jomendietad/access-control-stm32-esp32/esp32-s3-control-access-final/main/bsp/bsp_web.h

#ifndef BSP_WEB_H
#define BSP_WEB_H

#include <stdbool.h>

void BSP_Web_StartServer(void);
void BSP_Web_StopServer(void);
bool BSP_Web_IsResetRequested(void);
void BSP_Web_ClearResetRequest(void);

#endif /* BSP_WEB_H */
