jomendietad/access-control-stm32-esp32/esp32-s3-control-access-final/main/bsp/bsp_wifi.c

#include "bsp/bsp_wifi.h"
#include "esp_wifi.h"
#include "nvs_flash.h"
#include "esp_event.h"
#include "secrets/secrets.h"

static bool wifi_connected = false;

static void wifi_event_handler(void* arg, esp_event_base_t event_base, int32_t event_id, void* event_data) 
{
    if (event_base == WIFI_EVENT && event_id == WIFI_EVENT_STA_START) 
    {
        esp_wifi_connect();
    } 
    else if (event_base == WIFI_EVENT && event_id == WIFI_EVENT_STA_DISCONNECTED) 
    {
        wifi_connected = false;
        esp_wifi_connect();
    } 
    else if (event_base == IP_EVENT && event_id == IP_EVENT_STA_GOT_IP) 
    {
        wifi_connected = true;
    }
}

void BSP_WiFi_Init(void) 
{
    esp_netif_init();
    esp_event_loop_create_default();
    esp_netif_create_default_wifi_sta();
    
    wifi_init_config_t cfg = WIFI_INIT_CONFIG_DEFAULT();
    esp_wifi_init(&cfg);
    
    esp_event_handler_instance_register(WIFI_EVENT, ESP_EVENT_ANY_ID, &wifi_event_handler, NULL, NULL);
    esp_event_handler_instance_register(IP_EVENT, IP_EVENT_STA_GOT_IP, &wifi_event_handler, NULL, NULL);
    
    wifi_config_t wifi_config = {
        .sta = {
            .ssid = WIFI_SSID,
            .password = WIFI_PASS
        }
    };
    
    esp_wifi_set_mode(WIFI_MODE_STA);
    esp_wifi_set_config(WIFI_IF_STA, &wifi_config);
    esp_wifi_start();
}

bool BSP_WiFi_IsConnected(void) 
{
    return wifi_connected;
}
