jomendietad/access-control-stm32-esp32/stm32-nucleo-l476rg-control-access/src/bsp/bsp_placa.c

#include "bsp/bsp_placa.h"
#include "stm32l4xx_hal.h"
#include "bsp/bsp_uart.h"
#include "bsp/bsp_gpio.h"
#include "bsp/bsp_rfid.h"
#include "bsp/bsp_display.h"

static void SystemClock_Config(void);

void BSP_Init(void) {
    HAL_Init();
    SystemClock_Config();
    BSP_GPIO_Init();
    BSP_UART_Init();
    BSP_RFID_Init();
    BSP_Display_Init();
}

uint32_t BSP_GetTicks(void) {
    return HAL_GetTick();
}

static void SystemClock_Config(void) {
    RCC_OscInitTypeDef RCC_OscInitStruct = {0};
    RCC_ClkInitTypeDef RCC_ClkInitStruct = {0};

    RCC_OscInitStruct.OscillatorType = RCC_OSCILLATORTYPE_MSI;
    RCC_OscInitStruct.MSIState = RCC_MSI_ON;
    RCC_OscInitStruct.MSICalibrationValue = 0;
    RCC_OscInitStruct.MSIClockRange = RCC_MSIRANGE_6; // 4 MHz
    RCC_OscInitStruct.PLL.PLLState = RCC_PLL_ON;
    RCC_OscInitStruct.PLL.PLLSource = RCC_PLLSOURCE_MSI;
    RCC_OscInitStruct.PLL.PLLM = 1;
    RCC_OscInitStruct.PLL.PLLN = 40;
    RCC_OscInitStruct.PLL.PLLP = RCC_PLLP_DIV7;
    RCC_OscInitStruct.PLL.PLLQ = RCC_PLLQ_DIV2;
    RCC_OscInitStruct.PLL.PLLR = RCC_PLLR_DIV2;
    HAL_RCC_OscConfig(&RCC_OscInitStruct);

    RCC_ClkInitStruct.ClockType = RCC_CLOCKTYPE_HCLK|RCC_CLOCKTYPE_SYSCLK|RCC_CLOCKTYPE_PCLK1|RCC_CLOCKTYPE_PCLK2;
    RCC_ClkInitStruct.SYSCLKSource = RCC_SYSCLKSOURCE_PLLCLK;
    RCC_ClkInitStruct.AHBCLKDivider = RCC_SYSCLK_DIV1;
    RCC_ClkInitStruct.APB1CLKDivider = RCC_HCLK_DIV1;
    RCC_ClkInitStruct.APB2CLKDivider = RCC_HCLK_DIV1;
    HAL_RCC_ClockConfig(&RCC_ClkInitStruct, FLASH_LATENCY_4);
}

void SysTick_Handler(void) {
    HAL_IncTick();
}
